workinghard/BabyTV/Arduino/BabyTV_v1/imgFrog1.c

#ifndef IMG_FROG1
#define IMG_FROG1

#include <Arduino.h>

PROGMEM const byte frog1[768] = {
  4,8,64,4,8,64,4,8,64,4,8,64,4,8,64,4,8,64,4,8,64,4,8,64,4,8,64,4,8,64,4,8,64,4,8,64,4,8,64,4,8,64,4,8,64,4,8,64
,4,8,64,4,8,64,4,8,64,4,8,64,4,8,64,4,8,64,4,8,64,4,8,64,4,8,64,4,8,64,4,8,64,4,8,64,4,8,64,4,8,64,4,8,64,4,8,64
,4,8,64,4,8,64,4,8,64,4,8,64,4,8,64,4,8,64,4,8,64,4,8,64,4,8,64,4,8,64,4,8,64,4,8,64,4,8,64,4,8,64,4,8,64,4,8,64
,4,8,64,4,8,64,4,8,64,4,8,64,4,8,64,4,8,64,4,8,64,4,8,64,4,8,64,4,8,64,4,8,64,4,8,64,4,8,64,4,8,64,4,8,64,4,8,64
,4,8,64,4,8,64,4,8,64,8,200,8,4,8,64,4,8,64,252,240,0,8,200,8,252,240,0,252,240,0,4,8,64,4,8,64,8,200,8,4,8,64,4,8,64,4,8,64
,4,8,64,4,8,64,8,200,8,8,200,8,4,8,64,244,8,48,8,200,8,252,240,0,252,240,0,8,200,8,244,8,48,4,8,64,8,200,8,8,200,8,4,8,64,4,8,64
,4,8,64,4,8,64,4,8,64,8,200,8,4,8,64,8,200,8,8,200,8,252,240,0,252,240,0,8,200,8,8,200,8,4,8,64,8,200,8,4,8,64,4,8,64,4,8,64
,4,8,64,4,8,64,4,8,64,8,200,8,8,200,8,252,240,0,252,240,0,252,240,0,252,240,0,252,240,0,252,240,0,8,200,8,8,200,8,4,8,64,4,8,64,4,8,64
,4,8,64,4,8,64,4,8,64,4,8,64,4,8,64,252,240,0,8,200,8,252,240,0,252,240,0,252,240,0,252,240,0,4,8,64,4,8,64,4,8,64,4,8,64,4,8,64
,4,8,64,4,8,64,4,8,64,8,200,8,8,200,8,252,240,0,8,200,8,252,240,0,252,240,0,252,240,0,252,240,0,8,200,8,8,200,8,4,8,64,4,8,64,4,8,64
,4,8,64,4,8,64,4,8,64,8,200,8,4,8,64,8,200,8,252,240,0,8,200,8,252,240,0,252,240,0,8,200,8,4,8,64,8,200,8,4,8,64,4,8,64,4,8,64
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
,4,8,64,4,8,64,4,8,64,8,200,8,4,8,64,8,12,76,8,12,76,8,12,76,4,8,64,8,12,76,8,12,76,4,8,64,8,200,8,4,8,64,4,8,64,4,8,64
,4,8,64,4,8,64,4,8,64,4,8,64,4,8,64,8,12,76,8,12,76,4,8,64,4,8,64,8,12,76,8,12,76,4,8,64,4,8,64,4,8,64,4,8,64,4,8,64
,4,8,64,4,8,64,4,8,64,4,8,64,4,8,64,4,8,64,4,8,64,4,8,64,4,8,64,8,12,76,4,8,64,4,8,64,4,8,64,4,8,64,4,8,64,4,8,64
};
#endif
