workinghard/BabyTV/Arduino/BabyTV_v1/imgBat1.c

#ifndef IMG_BAT1
#define IMG_BAT1

#include <Arduino.h>
PROGMEM const byte bat1[768] = {
4,8,64,4,8,64,4,8,64,4,8,64,4,8,64,4,8,64,4,8,64,4,8,64,4,8,64,4,8,64,4,8,64,4,8,64,4,8,64,4,8,64,4,8,64,4,8,64
,4,8,64,4,8,64,4,8,64,4,8,64,4,8,64,4,8,64,4,8,64,156,156,160,4,8,64,156,160,160,4,8,64,4,8,64,4,8,64,4,8,64,4,8,64,4,8,64
,4,8,64,4,8,64,4,8,64,4,8,64,156,160,160,156,156,160,252,136,0,252,136,0,156,156,160,252,136,0,252,136,0,156,156,160,156,156,160,4,8,64,4,8,64,4,8,64
,4,8,64,4,8,64,4,8,64,4,8,64,4,8,64,156,160,160,252,136,0,252,136,0,156,156,160,252,136,0,252,136,0,156,156,160,4,8,64,4,8,64,4,8,64,4,8,64
,4,8,64,4,8,64,4,8,64,4,8,64,4,8,64,4,8,64,156,156,160,156,156,160,156,160,160,156,156,160,156,160,160,4,8,64,4,8,64,4,8,64,4,8,64,4,8,64
,4,8,64,4,8,64,4,8,64,4,8,64,156,156,160,156,156,160,252,232,0,252,236,0,156,156,160,252,232,0,252,236,0,156,156,160,156,156,160,4,8,64,4,8,64,4,8,64
,4,8,64,4,8,64,4,8,64,156,156,160,156,156,160,156,160,160,252,236,0,252,236,0,252,232,0,252,232,0,252,232,0,156,156,160,156,156,160,156,160,160,4,8,64,4,8,64
,4,8,64,156,160,160,156,156,160,156,160,160,156,156,160,156,156,160,252,232,0,252,232,0,252,232,0,252,232,0,252,236,0,156,160,160,156,156,160,156,156,160,156,160,160,156,160,160
,4,8,64,4,8,64,156,160,160,156,156,160,156,160,160,4,8,64,252,232,0,252,236,0,252,236,0,252,236,0,252,232,0,4,8,64,156,156,160,156,160,160,156,156,160,4,8,64
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
,4,8,64,156,160,160,156,160,160,156,156,160,156,156,160,4,8,64,4,8,64,4,8,64,4,8,64,4,8,64,4,8,64,4,8,64,156,160,160,156,156,160,156,156,160,156,160,160
,4,8,64,4,8,64,156,156,160,156,160,160,4,8,64,4,8,64,4,8,64,4,8,64,4,8,64,4,8,64,4,8,64,4,8,64,4,8,64,156,156,160,156,160,160,4,8,64
};
#endif
