workinghard/BabyTV/Arduino/BabyTV_v1/imgBee1.c

#ifndef IMG_BEE1
#define IMG_BEE1

#include <Arduino.h>

PROGMEM const byte bee1 [768] = {
4,8,64,4,8,64,4,8,64,4,8,64,4,8,64,4,8,64,4,8,64,4,8,64,4,8,64,4,8,64,4,8,64,4,8,64,4,8,64,4,8,64,4,8,64,4,8,64
,4,8,64,4,8,64,4,8,64,4,8,64,4,8,64,4,8,64,4,8,64,4,8,64,4,8,64,4,8,64,4,8,64,4,8,64,4,8,64,4,8,64,4,8,64,4,8,64
,4,8,64,4,8,64,4,8,64,4,8,64,4,8,64,4,8,64,4,8,64,4,8,64,4,8,64,4,8,64,4,8,64,4,8,64,4,8,64,4,8,64,4,8,64,4,8,64
,4,8,64,4,8,64,4,8,64,4,8,64,252,252,252,4,8,64,4,8,64,4,8,64,252,224,0,4,8,64,4,8,64,4,8,64,252,252,252,4,8,64,4,8,64,4,8,64
,4,8,64,4,8,64,4,8,64,4,8,64,252,252,252,4,8,64,252,224,0,252,120,0,252,224,0,252,120,0,252,224,0,4,8,64,252,252,252,4,8,64,4,8,64,4,8,64
,4,8,64,4,8,64,4,8,64,4,8,64,4,8,64,252,252,252,252,120,0,252,120,0,252,224,0,252,120,0,252,120,0,252,252,252,4,8,64,4,8,64,4,8,64,4,8,64
,4,8,64,4,8,64,4,8,64,4,8,64,4,8,64,4,8,64,252,224,0,252,224,0,252,224,0,252,224,0,252,224,0,4,8,64,4,8,64,4,8,64,4,8,64,4,8,64
,4,8,64,4,8,64,4,8,64,4,8,64,4,8,64,252,252,252,252,252,252,252,224,0,252,224,0,252,224,0,252,252,252,252,252,252,4,8,64,4,8,64,4,8,64,4,8,64
,4,8,64,4,8,64,4,8,64,4,8,64,4,8,64,252,252,252,252,252,252,252,120,0,252,120,0,252,120,0,252,252,252,252,252,252,4,8,64,4,8,64,4,8,64,4,8,64
,4,8,64,4,8,64,4,8,64,4,8,64,252,252,252,252,252,252,4,8,64,252,120,0,252,120,0,252,120,0,4,8,64,252,252,252,252,252,252,4,8,64,4,8,64,4,8,64
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
,4,8,64,4,8,64,4,8,64,4,8,64,4,8,64,4,8,64,4,8,64,4,8,64,4,8,64,4,8,64,4,8,64,4,8,64,4,8,64,4,8,64,4,8,64,4,8,64
,4,8,64,4,8,64,4,8,64,4,8,64,4,8,64,4,8,64,4,8,64,4,8,64,4,8,64,4,8,64,4,8,64,4,8,64,4,8,64,4,8,64,4,8,64,4,8,64
};
#endif
