workinghard/BabyTV/Arduino/BabyTV_v1/imgMushroom1.c

#ifndef IMG_MUSHROOM1
#define IMG_MUSHROOM1

#include <Arduino.h>
PROGMEM const byte mushroom1 [768] = {
  0,0,0,0,0,0,0,0,0,0,0,0,0,0,0,0,0,0,252,0,0,252,0,0,252,0,0,252,0,0,0,0,0,0,0,0,0,0,0,0,0,0,0,0,0,0,0,0
,0,0,0,0,0,0,0,0,0,0,0,0,0,0,0,252,0,0,252,0,0,252,0,0,252,0,0,252,0,0,252,0,0,0,0,0,0,0,0,0,0,0,0,0,0,0,0,0
,0,0,0,0,0,0,0,0,0,0,0,0,252,0,0,252,0,0,252,0,0,252,0,0,252,0,0,252,0,0,252,0,0,252,0,0,0,0,0,0,0,0,0,0,0,0,0,0
,0,0,0,0,0,0,0,0,0,252,0,0,252,0,0,252,0,0,252,0,0,252,0,0,252,0,0,252,0,0,252,0,0,252,0,0,252,0,0,0,0,0,0,0,0,0,0,0
,0,0,0,0,0,0,252,0,0,8,12,76,8,12,76,252,0,0,252,0,0,252,0,0,252,0,0,252,0,0,252,0,0,8,12,76,8,12,76,252,0,0,0,0,0,0,0,0
,0,0,0,252,0,0,252,0,0,252,0,0,252,252,252,8,12,76,252,0,0,252,0,0,252,0,0,252,0,0,8,12,76,252,252,252,252,0,0,252,0,0,0,0,0,0,0,0
,0,0,0,252,0,0,252,0,0,252,0,0,252,252,252,8,12,76,8,12,76,8,12,76,8,12,76,8,12,76,8,12,76,252,252,252,252,0,0,252,0,0,252,0,0,0,0,0
,252,0,0,252,0,0,252,0,0,252,0,0,252,252,252,8,12,76,252,252,252,252,0,0,252,0,0,252,252,252,8,12,76,252,252,252,252,0,0,252,0,0,252,0,0,252,0,0
,252,0,0,252,0,0,252,0,0,252,0,0,252,252,252,252,252,252,252,252,252,252,0,0,252,0,0,252,252,252,252,252,252,252,252,252,252,0,0,252,0,0,252,0,0,252,0,0
,252,0,0,252,0,0,252,0,0,252,0,0,252,0,0,252,0,0,252,0,0,252,0,0,252,0,0,252,0,0,252,0,0,252,0,0,252,0,0,252,0,0,252,0,0,252,0,0
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
,0,0,0,8,12,76,8,12,76,8,12,76,8,12,76,8,12,76,8,12,76,252,252,252,252,252,252,252,252,252,8,12,76,8,12,76,8,12,76,0,0,0,0,0,0,0,0,0
,0,0,0,0,0,0,8,12,76,8,12,76,8,12,76,8,12,76,8,12,76,0,0,0,0,0,0,8,12,76,8,12,76,8,12,76,0,0,0,0,0,0,0,0,0,0,0,0
};
#endif
